timmy-quinn/led-matrix/01_demos/multi_mode/plasma_state.cpp

// Plasma effect derived from code found here https://github.com/meharjit/ledtable
// More info can be found https://en.wikipedia.org/wiki/Plasma_effect
#include "plasma_state.h"
#include "led_matrix.h"
#include <math.h>
#define FRAME_SCALE 0.3
#define INCREMENT_MAX 0xffff

static uint16_t float_hue_to_u16(float hue) {
  return (hue * (0xffff/2)) + 0xffff/2; 
}

static uint16_t get_pixel_color(Adafruit_NeoPixel *pixels, float x_base, float y_base) {
  float hue; 
  float x = x_base * (2 * 3.1415) / PIXEL_COLUMNS * FRAME_SCALE; 
  float y = y_base * (2 * 3.1415) / PIXEL_ROWS * FRAME_SCALE; 
  float scale = 0.7; 

  hue = sin(x -y);
  hue += sin(x * x - (y * y * 2)); 
  hue+=sin(y-x); 
  hue /=3;  
  return float_hue_to_u16(hue); 
  

}

static void calc_frame(uint16_t hue_offset, float phase, Adafruit_NeoPixel *pixels) {
  float x_norm, y_norm;
  uint16_t hue;
  uint32_t color;

    for (int x = 0; x < PIXEL_COLUMNS; x++) {
        for (int y = 0; y < PIXEL_ROWS; y++) {
            hue = get_pixel_color(pixels, x * phase, y * (-1 *phase)); 
            color = pixels->ColorHSV(hue + hue_offset); 
            setArrColor(pixels, y, x, color);
        }
    }
    pixels->show();
    delay(10);
}

void plasma_state :: update() {
  static uint16_t hue_offset = 0; 
  static float phase = -2.0; 
  static const float step = 0.02;

  calc_frame(hue_offset, 1 - fabsf(phase), mPixels);
  phase+=step; 

  if(phase > 2.0) {
    hue_offset += 2048;
    phase = -2.0;
  }

}
